yoyoslayer/Tamagotchi-Device/Images/3D File Export Back.png

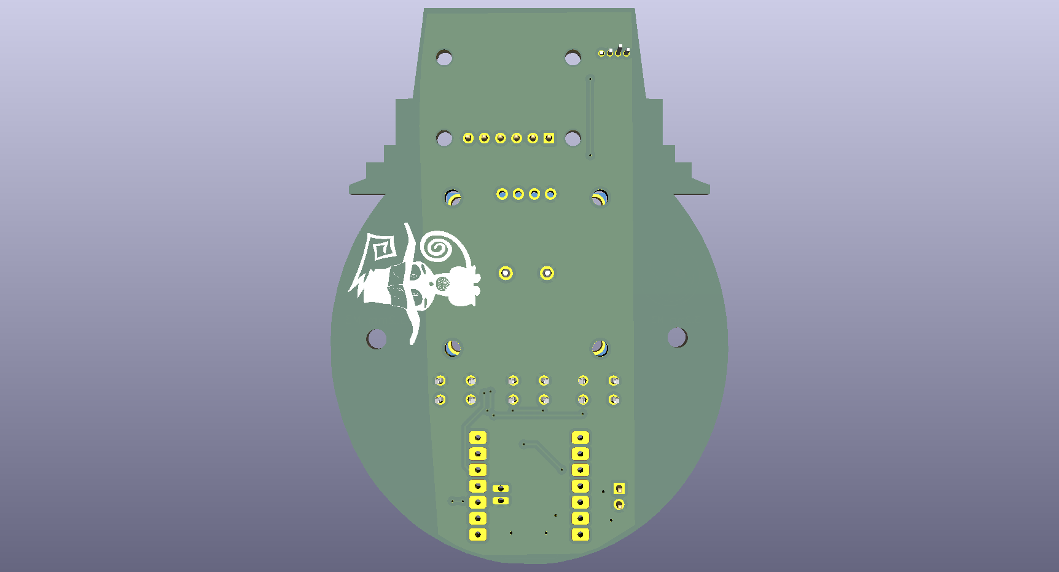
Images/3D File Export Back.png
